radupascale/smartwatch-licenta/board/proto/docs/route_v1/3d_back.png

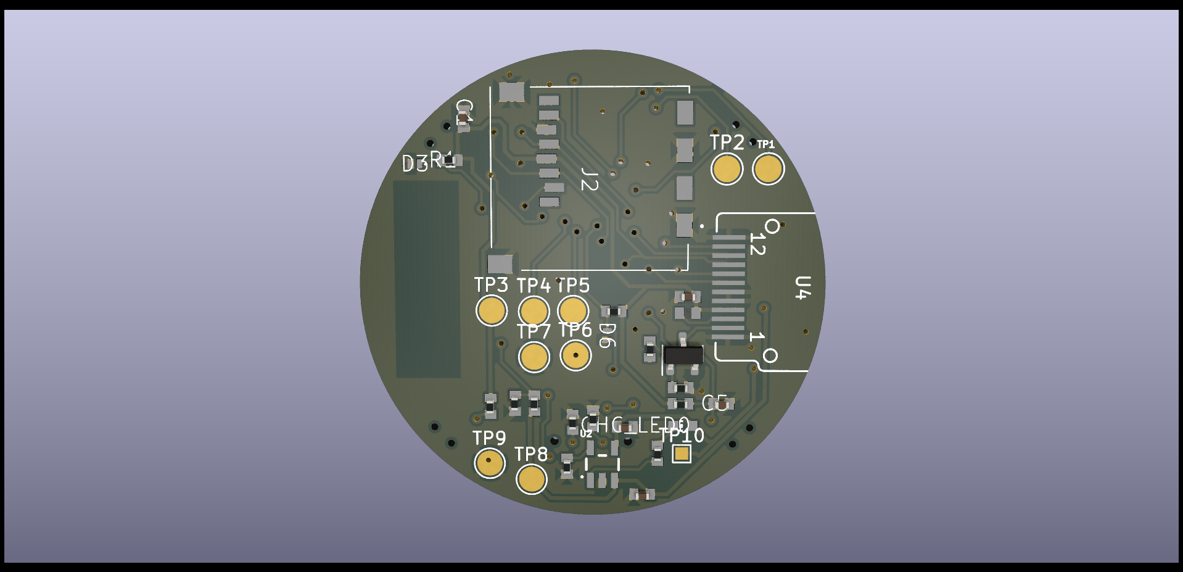
board/proto/docs/route_v1/3d_back.png
