radupascale/smartwatch-licenta/CAD/components/MCP73831T-2ACI_OT.STEP

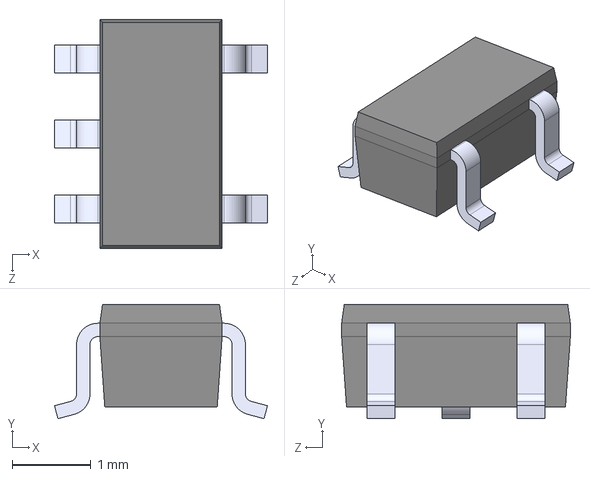
[picture p22: CAD file, 2024-03-10]
CAD/components/MCP73831T-2ACI_OT.STEP
2.70 x 1.45 x 2.90 mm
